hybo-ilidar/hybohat/datasheets/modules/dims2-esp32-maybe-wrong.jpg

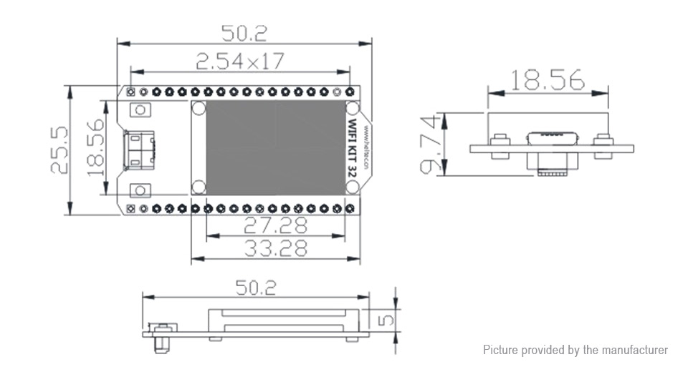
datasheets/modules/dims2-esp32-maybe-wrong.jpg
