hybo-ilidar/hybohat/datasheets/modules/dims-arduino-uno-correct.png

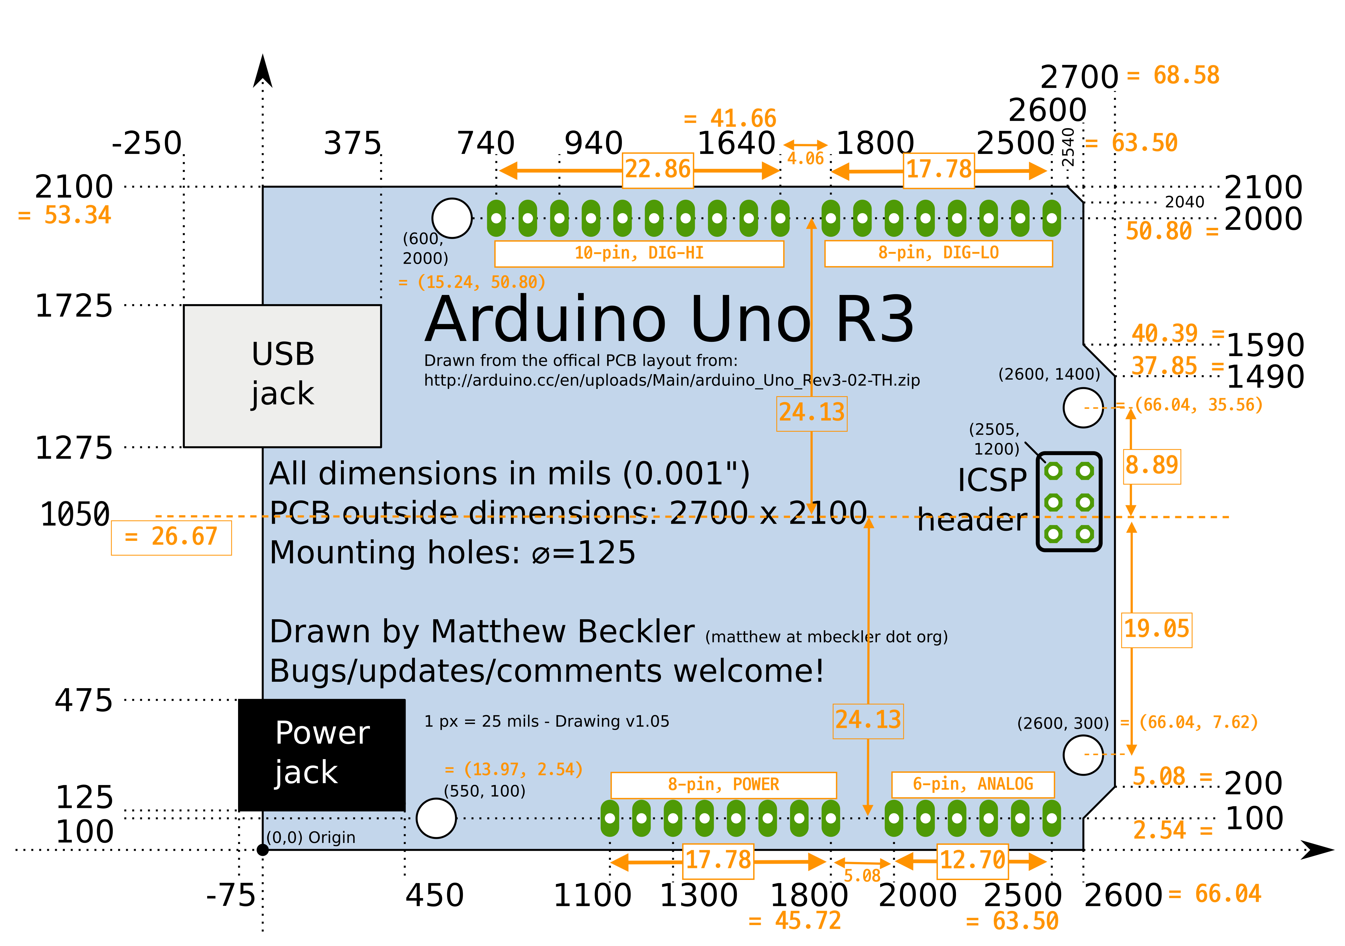
datasheets/modules/dims-arduino-uno-correct.png
