hybo-ilidar/hybohat/datasheets/modules/dims-esp32c-devkit-2d-model.png

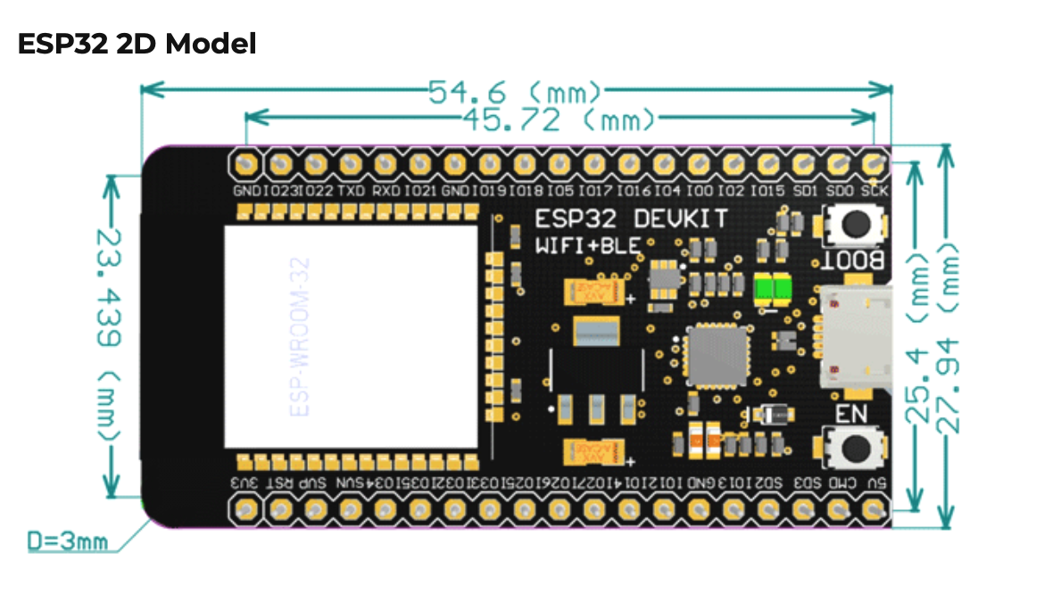
datasheets/modules/dims-esp32c-devkit-2d-model.png
