hybo-ilidar/hybohat/images/hybohat-assy-bottom.jpg

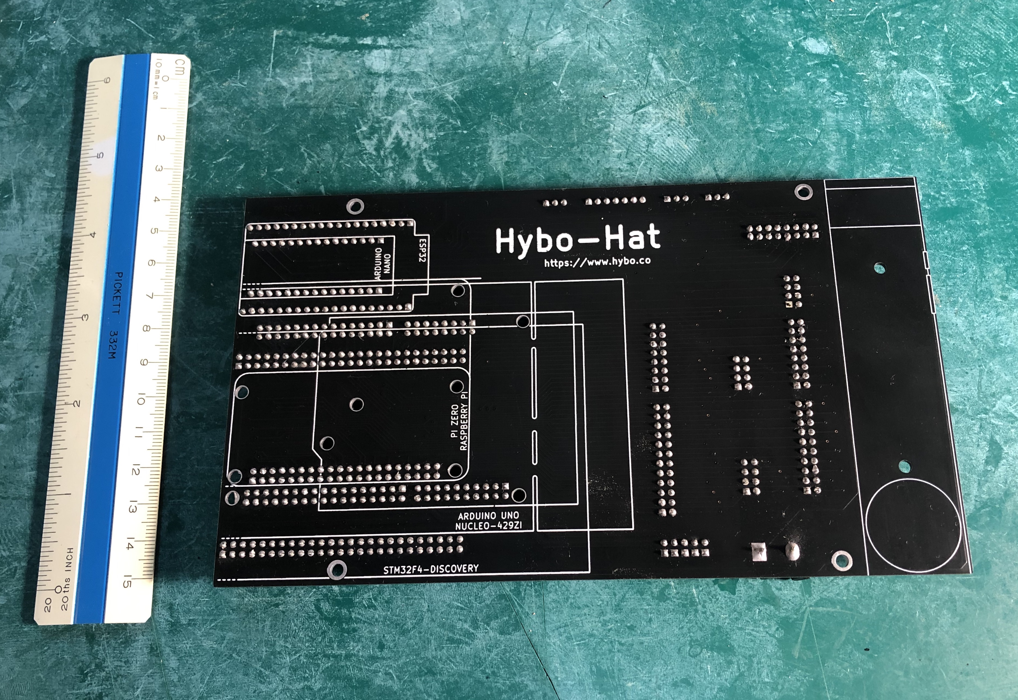
images/hybohat-assy-bottom.jpg
